RoguedBear/esp32-touch-ble-keyboard/include/KEY_CONFIG.h

#ifndef __KEY_CONFIG_h
#define __KEY_CONFIG_h
#include "TouchKey.h"
TouchKey TOUCH_KEYS[] = {TouchKey(T9, '2', 35), TouchKey(T7, 'w'),
                         TouchKey(T5, 's'), TouchKey(T3, 'x')};
#endif
